Jack-Birtles/IDENTIDEM.design-MRF2/3MF/Main Parts/advance-lever.3mf

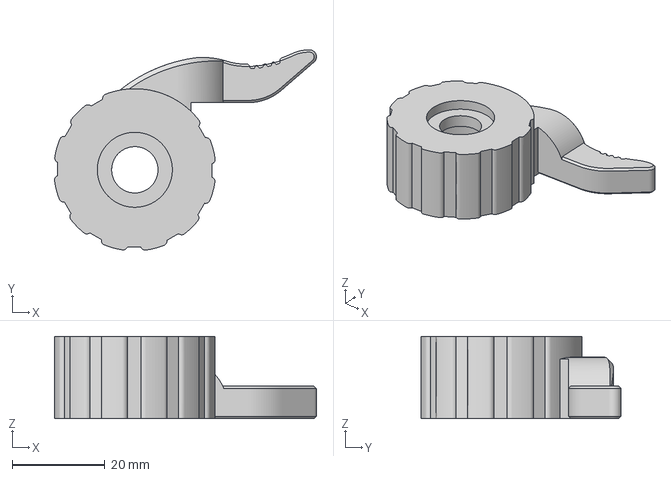
[picture p15: CAD file, 2026-02-24]
3MF/Main Parts/advance-lever.3mf
56.6 x 43.2 x 17.8 mm
