Jack-Birtles/IDENTIDEM.design-MRF2/3MF/Bayonet Lens Cone/lens-center-ring.3mf

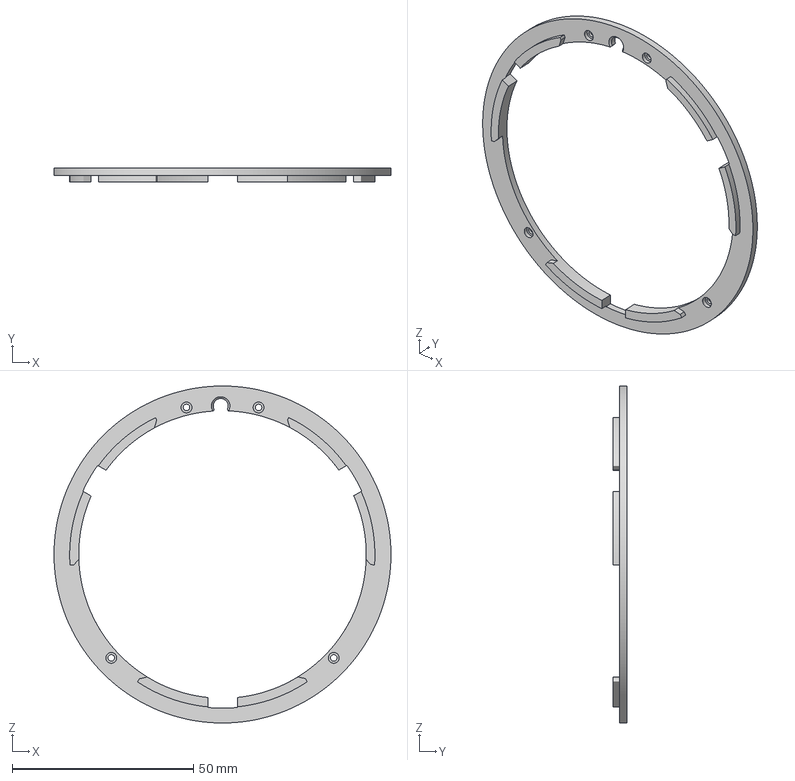
[picture p16: CAD file, 2026-02-24]
3MF/Bayonet Lens Cone/lens-center-ring.3mf
93.0 x 3.75 x 93.0 mm
