Jack-Birtles/IDENTIDEM.design-MRF2/3MF/Film Masks/6x9.3mf

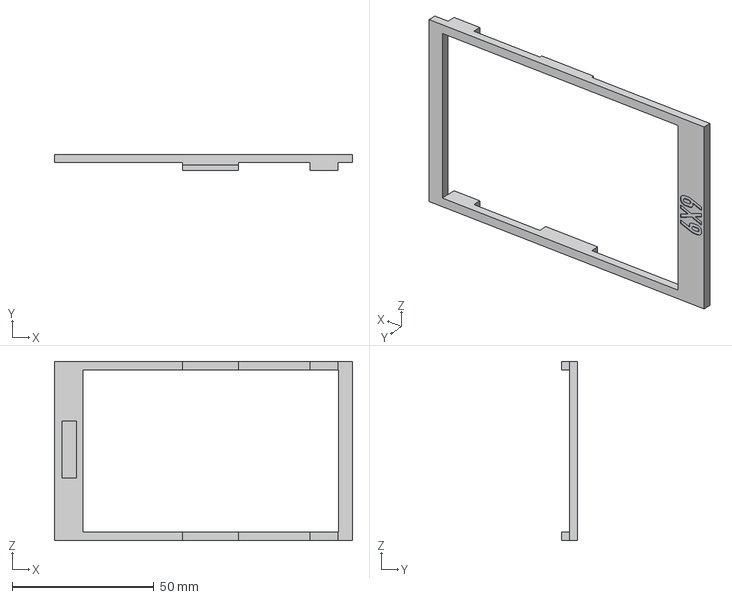
[picture p17: CAD file, 2026-02-24]
3MF/Film Masks/6x9.3mf
105.0 x 5.65 x 63.2 mm
