Jack-Birtles/IDENTIDEM.design-MRF2/3MF/Fine Parts/lidar-sensor-holder.3mf

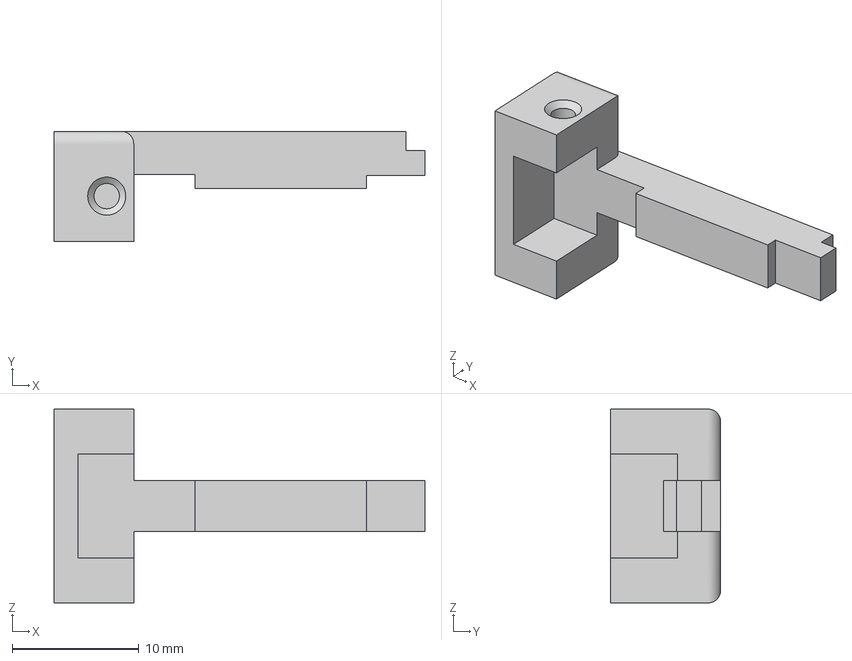
[picture p18: CAD file, 2026-02-24]
3MF/Fine Parts/lidar-sensor-holder.3mf
29.2 x 8.70 x 15.3 mm
