Jack-Birtles/IDENTIDEM.design-MRF2/3MF/Main Parts/middle-plate.3mf

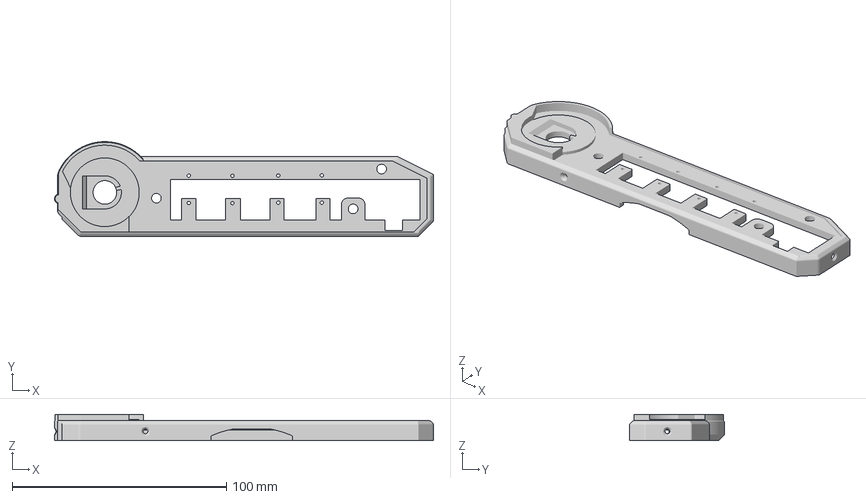
[picture p19: CAD file, 2026-02-24]
3MF/Main Parts/middle-plate.3mf
176.7 x 44.2 x 12.3 mm
