Jack-Birtles/IDENTIDEM.design-MRF2/3MF/Bayonet Lens Cone/lens-top-ring.3mf

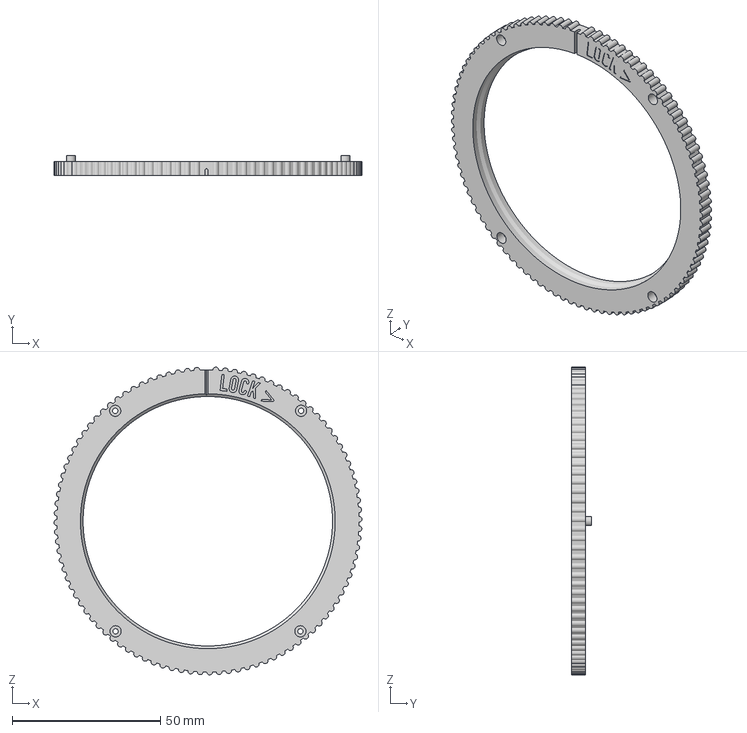
[picture p20: CAD file, 2026-02-24]
3MF/Bayonet Lens Cone/lens-top-ring.3mf
104.0 x 6.83 x 103.9 mm
