Jack-Birtles/IDENTIDEM.design-MRF2/3MF/Fine Parts/spring-ring.3mf

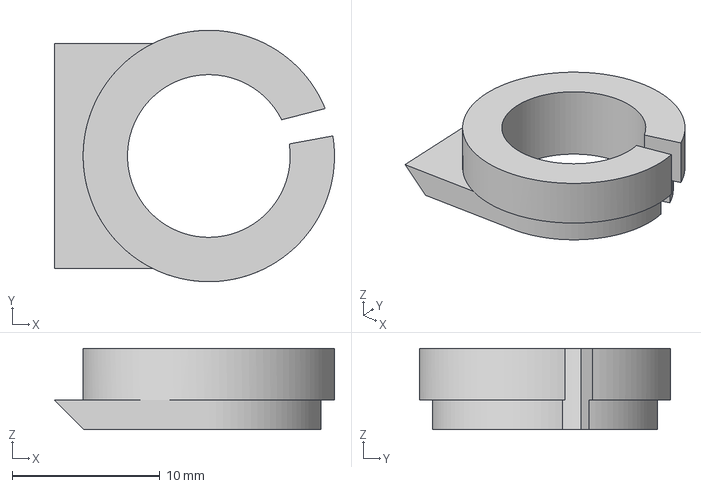
[picture p22: CAD file, 2026-02-24]
3MF/Fine Parts/spring-ring.3mf
18.9 x 17.0 x 5.50 mm
