Jack-Birtles/IDENTIDEM.design-MRF2/3MF/Main Parts/viewfinder-body.3mf

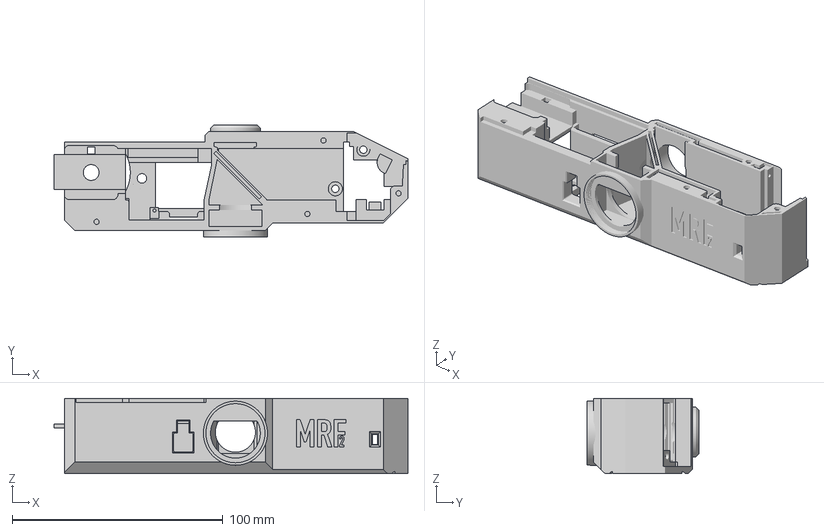
[picture p23: CAD file, 2026-02-24]
3MF/Main Parts/viewfinder-body.3mf
168.0 x 53.1 x 35.6 mm
