Jack-Birtles/IDENTIDEM.design-MRF2/3MF/Fine Parts/advance-post-top.3mf

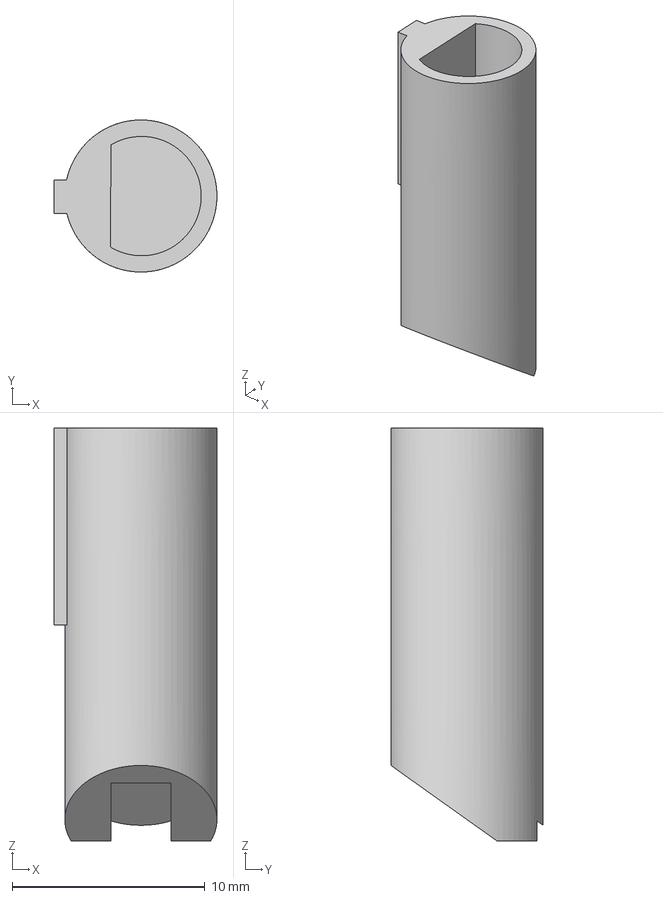
[picture p25: CAD file, 2026-02-24]
3MF/Fine Parts/advance-post-top.3mf
8.46 x 7.90 x 21.5 mm
