Jack-Birtles/IDENTIDEM.design-MRF2/3MF/Main Parts/door-back.3mf

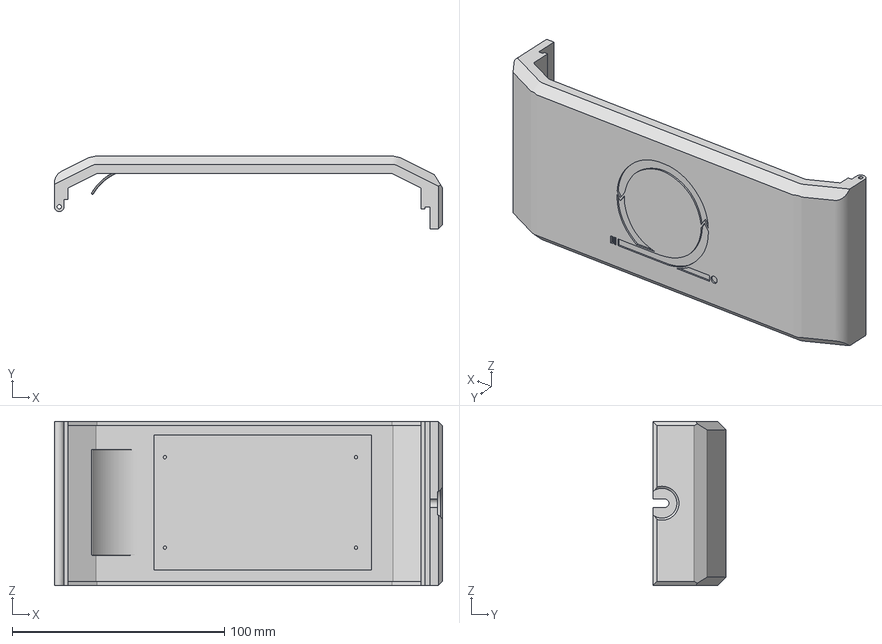
[picture p26: CAD file, 2026-02-24]
3MF/Main Parts/door-back.3mf
182.8 x 34.6 x 77.3 mm
