Jack-Birtles/IDENTIDEM.design-MRF2/3MF/Film Masks/9x3.3mf

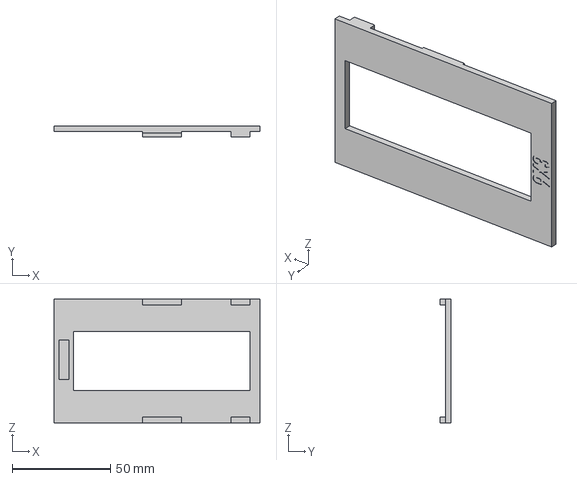
[picture p27: CAD file, 2026-02-24]
3MF/Film Masks/9x3.3mf
105.0 x 5.65 x 63.2 mm
