Jack-Birtles/IDENTIDEM.design-MRF2/3MF/Fine Parts/advance-pin.3mf

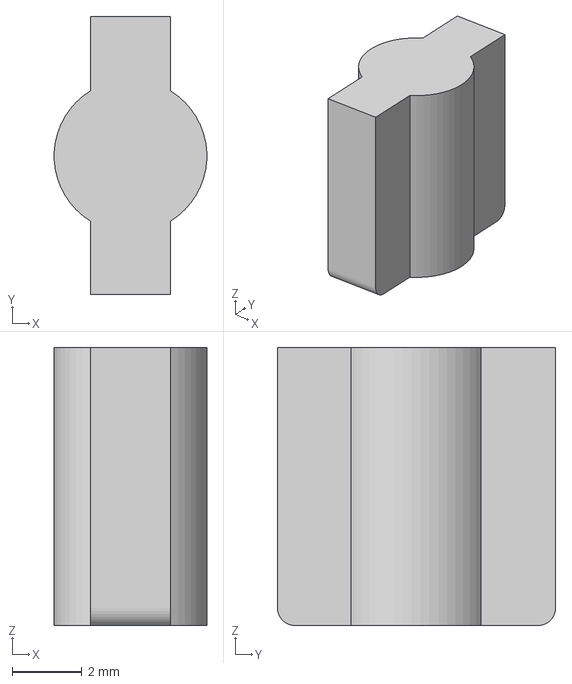
[picture p28: CAD file, 2026-02-24]
3MF/Fine Parts/advance-pin.3mf
4.39 x 8.00 x 8.00 mm
