Jack-Birtles/IDENTIDEM.design-MRF2/3MF/Main Parts/camera-body.3mf

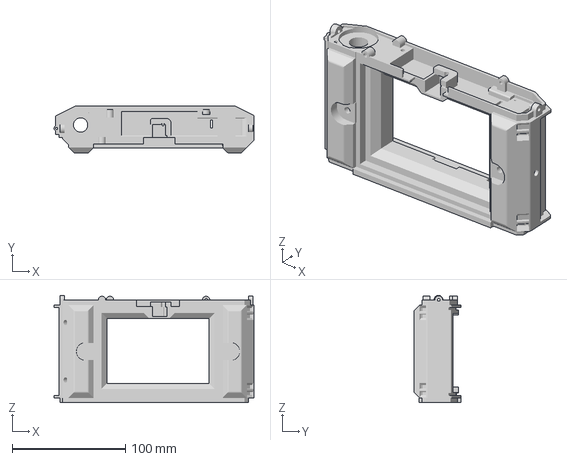
[picture p29: CAD file, 2026-02-24]
3MF/Main Parts/camera-body.3mf
176.7 x 41.5 x 94.8 mm
