Jack-Birtles/IDENTIDEM.design-MRF2/3MF/Fine Parts/advance-spring-cap.3mf

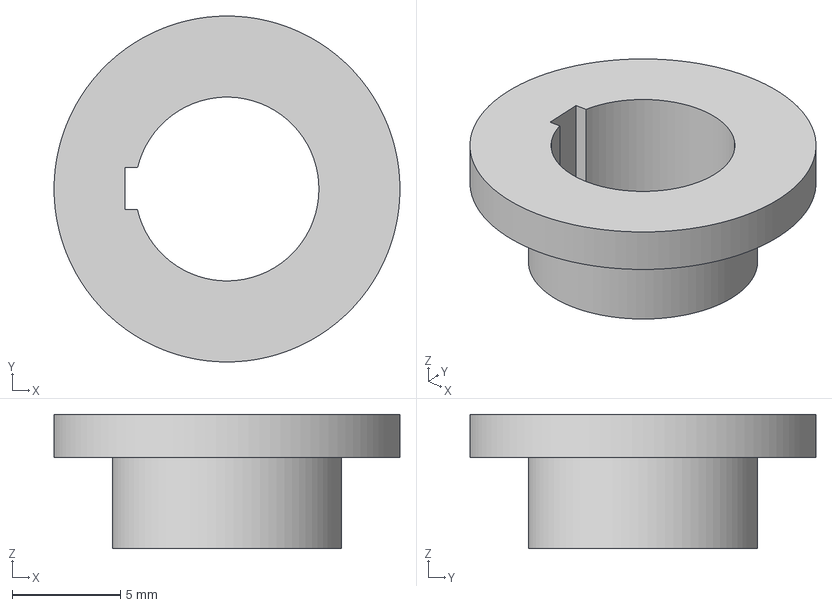
[picture p30: CAD file, 2026-02-24]
3MF/Fine Parts/advance-spring-cap.3mf
16.0 x 16.0 x 6.21 mm
