Jack-Birtles/IDENTIDEM.design-MRF2/3MF/Main Parts/body-bottom.3mf

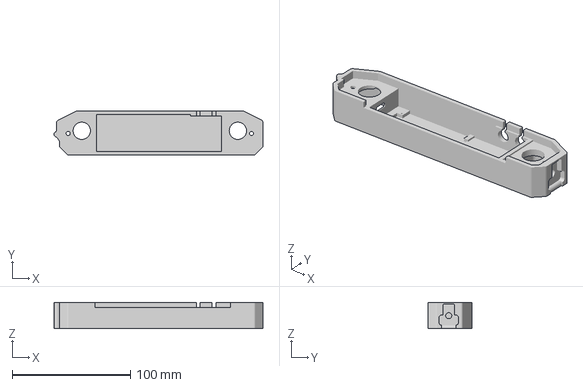
[picture p31: CAD file, 2026-02-07]
3MF/Main Parts/body-bottom.3mf
176.7 x 37.2 x 22.0 mm
