Jack-Birtles/IDENTIDEM.design-MRF2/3MF/Fine Parts/advance-ratchet.3mf

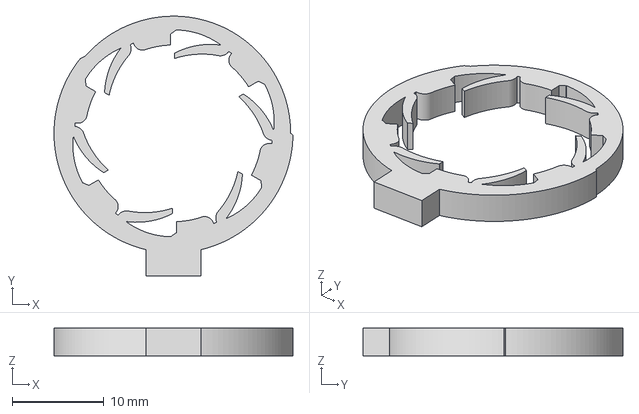
[picture p32: CAD file, 2026-02-24]
3MF/Fine Parts/advance-ratchet.3mf
26.0 x 28.2 x 3.00 mm
