Jack-Birtles/IDENTIDEM.design-MRF2/3MF/Fine Parts/left (from back) spool.3mf

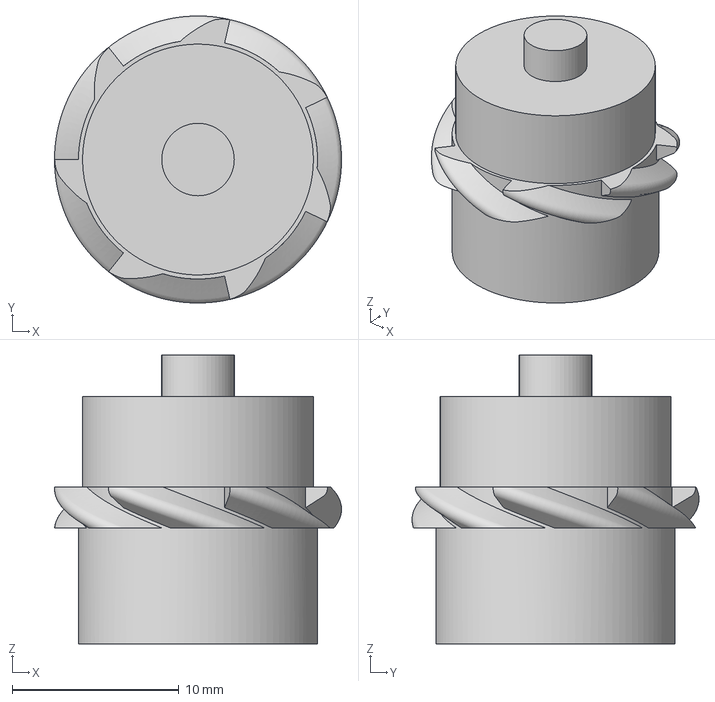
[picture p33: CAD file, 2026-02-24]
3MF/Fine Parts/left (from back) spool.3mf
17.2 x 17.2 x 17.3 mm
