Jack-Birtles/IDENTIDEM.design-MRF2/3MF/Fine Parts/right (from back) spool.3mf

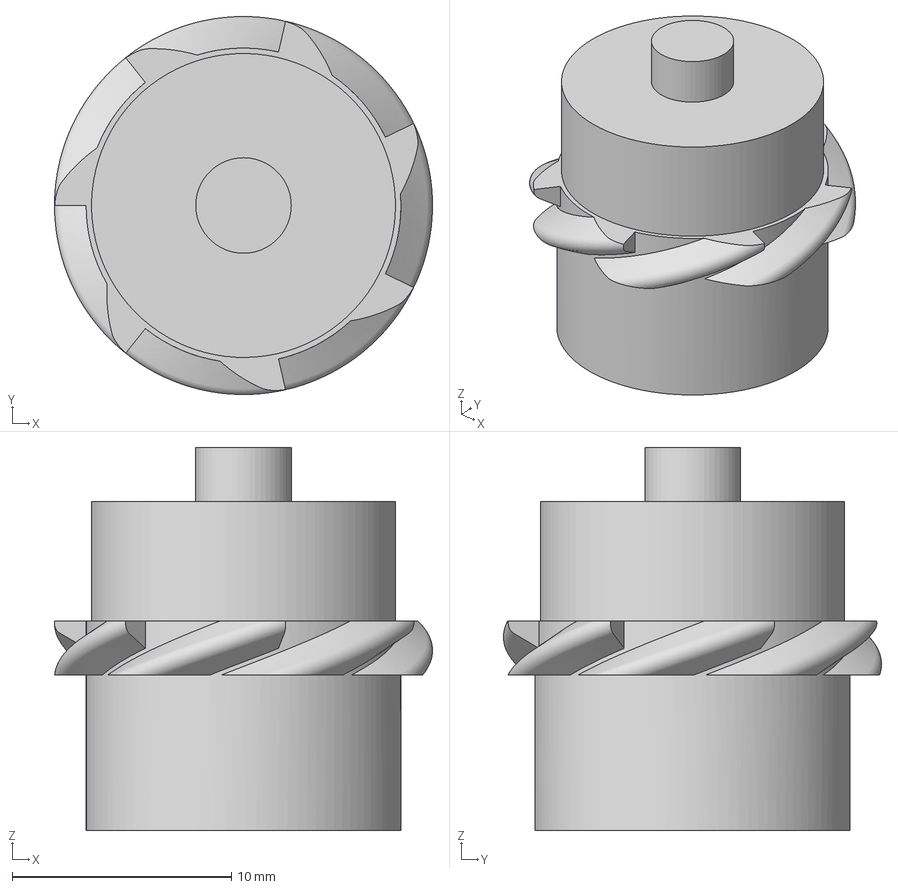
[picture p34: CAD file, 2026-02-24]
3MF/Fine Parts/right (from back) spool.3mf
17.2 x 17.2 x 17.5 mm
