Jack-Birtles/IDENTIDEM.design-MRF2/3MF/Fine Parts/spool-key (optional).3mf

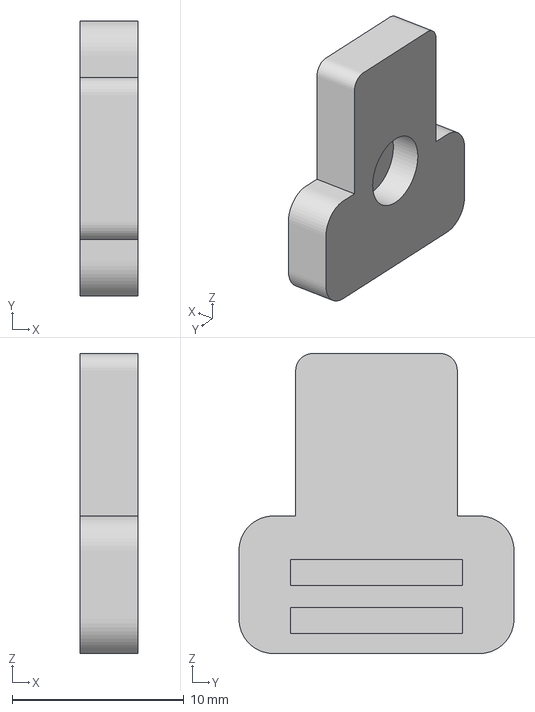
[picture p35: CAD file, 2026-02-24]
3MF/Fine Parts/spool-key (optional).3mf
3.38 x 16.0 x 17.5 mm
