Jack-Birtles/IDENTIDEM.design-MRF2/3MF/Fine Parts/advance-post-bottom.3mf

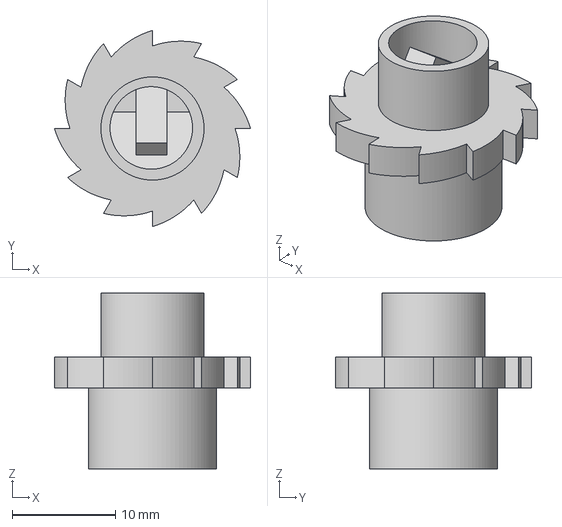
[picture p36: CAD file, 2026-02-24]
3MF/Fine Parts/advance-post-bottom.3mf
19.0 x 19.0 x 17.0 mm
