Jack-Birtles/IDENTIDEM.design-MRF2/Firmware/include/lidar_logic.h

#ifndef LIDAR_LOGIC_H
#define LIDAR_LOGIC_H

#include <stddef.h>
#include <stdint.h>
#include <DTS6012M_UART.h>

struct LidarCandidate
{
  bool valid;
  int distance_cm;
  int confidence;
  int quality_level; // 1..4 (poor..excellent), 0 when invalid
};

// offset_delta_cm is the difference between the configured geometry-offset
// pref and the default it was calibrated with, in cm:
// (lidar_distance_offset_mm - DEFAULT_LIDAR_DISTANCE_OFFSET_MM) / 10.
LidarCandidate chooseBestLidarCandidate(const DTSMeasurement &measurement,
                                        int previous_distance_cm,
                                        bool has_lens_prior,
                                        int lens_prior_cm,
                                        int offset_delta_cm = 0);

int blendLidarDistance(int previous_distance_cm, int next_distance_cm, int confidence);

// SNR in permille: primary intensity relative to the sensor's ambient-light
// baseline (sunlightBase). Returns -1 when there is no baseline (sunlightBase
// == 0), signalling the caller to skip SNR-based logic. Exposed for the
// diagnostics screen and unit tests.
int computeSnrPermille(uint16_t intensity, uint16_t sunlight_base);

// Near-range distance correction (cm). Below LIDAR_CAL_CUTOFF_CM the dToF sensor
// over-reads, so a single-reference power law pulls the value toward truth. The
// correction is bounded: it can never return less than LIDAR_CAL_MIN_OUTPUT_PCT
// percent of the raw distance (interim guard pending the measured table, bd 4p9),
// so real sub-metre subjects are not collapsed below the display floor. Values at
// or above the cutoff pass through unchanged. Exposed for the diagnostics screen
// and unit tests. The correction anchor was measured with the default geometry
// offset; pass offset_delta_cm (configured minus default, in cm) so the
// correction is evaluated in the default-offset frame and the delta re-added,
// keeping the anchor valid when the user tunes the offset pref.
int applyLidarCalibrationCm(int raw_cm, int offset_delta_cm = 0);

// True when the LiDAR reading is so far beyond the lens focus prior that it is
// almost certainly a beam-miss (LiDAR found distant background past the framed
// subject). Asymmetric: only flags overshoot, not undershoot. Returns false
// when the lens is focused beyond the near-range gate threshold or no prior is
// available. The allowed overshoot scales with the prior, since parallax
// beam-miss error grows with distance; a confident return (quality_level >=
// LIDAR_PLAUSIBILITY_TRUST_QUALITY_LEVEL) earns a wider but still finite
// allowance, so a gross overshoot is gated even when graded GOOD/EXCELLENT.
bool isLidarReadingImplausible(int lidar_distance_cm, int lens_prior_cm, int quality_level);

// Running state for the plausibility-gate hold. The gate rejects readings that
// overshoot the lens prior and holds the previous value; this tracks how long
// the current overshoot has persisted and whether the rejected readings are
// settling on a consistent value (a deliberate re-aim) or are jumpy (a true
// beam-miss past the subject).
struct PlausibilityHoldState
{
  int rejectedFrames = 0;   // consecutive implausible frames in this hold
  int consistentFrames = 0; // consecutive implausible frames agreeing with the last
  int lastRejectedCm = 0;   // distance of the previous implausible reading (0 = none yet)
};

// Feed one implausible reading into the hold state and decide whether to release
// (accept) it. Releases when the rejected readings have settled within
// stable_delta_cm for stable_release_frames in a row (deliberate re-aim at a
// real far subject), or when max_hold_frames is reached (safety cap so a noisy
// beam-miss can never pin the readout to a stale value forever).
bool updatePlausibilityHold(PlausibilityHoldState &state,
                            int reading_cm,
                            int stable_delta_cm,
                            int stable_release_frames,
                            int max_hold_frames);

// Clear the hold state. Call when a plausible reading arrives.
void resetPlausibilityHold(PlausibilityHoldState &state);

// Add a confidence boost once the LiDAR has locked onto a stable subject
// (consecutive frames within LIDAR_STABLE_DELTA_CM of each other). Caller
// tracks the streak count; this function applies the boost and clamps the
// result so a marginal reading cannot be promoted to excellent.
int applyStableConfidenceBoost(int base_confidence, int stable_streak_frames);

// Hysteresis-based update for the "ambient IR is high enough to degrade the
// LiDAR" warning state. Caller passes the current state and the sensor's
// sunlight base; returns the next state. Stays on between EXIT and ENTER
// thresholds so the indicator does not flicker.
bool updateSunlightWarnState(bool currently_warning, uint16_t sunlight_base);

void formatDistanceDisplay(int corrected_cm, char *buffer, size_t bufferSize);

// Placeholder shown when the sensor stops returning data. "Inf?" when the last
// accepted reading was at or beyond LIDAR_FAR_SIGNAL_LOSS_CM — no return at
// that range usually means the user re-aimed at the sky — and "..." otherwise.
// Deliberately distinct from the "Inf." that formatDistanceDisplay() emits for
// a genuine measured reading, so a dropout can't be read as a measurement.
// current_display is the string currently on screen: once it already marks a far
// dropout ("Inf?"/"Inf."), the placeholder stays "Inf?" so the far state survives
// clearLidarDisplay() zeroing prev_distance between frames. Pass nullptr to decide
// purely from prev_distance_cm.
const char *lidarSignalLossPlaceholder(int prev_distance_cm, const char *current_display);

// Format the age of the last LiDAR telemetry frame for the diagnostics screen:
// "--" when no frame has been captured yet (telemetry_ms == 0 sentinel),
// "NNNms" under one second, "N.Ns" up to 99s, ">99s" beyond. Takes uint32_t so
// the unsigned subtraction survives a millis() wrap on target and host alike.
void formatLidarTelemetryAge(uint32_t now_ms, uint32_t telemetry_ms, char *buffer, size_t bufferSize);

#endif // LIDAR_LOGIC_H
