Jack-Birtles/IDENTIDEM.design-MRF2/Firmware/src/lidar_recovery_logic.cpp

#include "lidar_recovery_logic.h"

#include <Arduino.h>

#include "mrfconstants.h"

namespace
{
unsigned long computeRecoveryBackoffMs(int consecutiveErrors)
{
  unsigned long delayMs = LIDAR_RECOVERY_RETRY_BASE_MS;
  int attempts = min(consecutiveErrors, 6);
  for (int i = 1; i < attempts; i++)
  {
    delayMs = min(delayMs * 2UL, LIDAR_RECOVERY_RETRY_MAX_MS);
  }
  return delayMs;
}
} // namespace

LidarRecoveryEvent lidarRecoveryEventForUpdateError(DTSError update_error)
{
  // NO_NEW_DATA (v2.6.0+) is returned whenever no complete frame arrived this
  // poll — the normal case every time the loop runs faster than the sensor's
  // frame rate. Like a genuine TIMEOUT it must map to the TIME-based TIMEOUT
  // event, which only escalates to recovery after LIDAR_RECOVERY_TIMEOUT_MS of no
  // valid data. It must NOT map to the COUNT-based ERROR event: three fast no-data
  // polls would otherwise cross LIDAR_RECOVERY_ERROR_THRESHOLD in milliseconds and
  // trip spurious recovery on a perfectly healthy sensor. Real frame faults (CRC,
  // framing, buffer overflow) still map to ERROR.
  switch (update_error)
  {
    case DTSError::NO_NEW_DATA:
    case DTSError::TIMEOUT:
      return LidarRecoveryEvent::TIMEOUT;
    default:
      return LidarRecoveryEvent::ERROR;
  }
}

void resetLidarRecoveryState(LidarRecoveryState &state, unsigned long now_ms)
{
  state.initialized = true;
  state.recovering = false;
  state.consecutive_errors = 0;
  state.last_valid_measurement_ms = now_ms;
  state.last_frame_ms = now_ms;
  state.next_recovery_attempt_ms = now_ms;
}

LidarRecoveryDecision updateLidarRecoveryState(
    LidarRecoveryState &state, LidarRecoveryEvent event, unsigned long now_ms)
{
  if (!state.initialized)
  {
    resetLidarRecoveryState(state, now_ms);
  }

  if (event == LidarRecoveryEvent::VALID_MEASUREMENT)
  {
    state.recovering = false;
    state.consecutive_errors = 0;
    state.last_valid_measurement_ms = now_ms;
    state.last_frame_ms = now_ms;
    state.next_recovery_attempt_ms = now_ms;
    return {false, false};
  }

  if (event == LidarRecoveryEvent::NO_VALID_MEASUREMENT)
  {
    // A well-formed frame arrived but its candidate was gated out. The link
    // is healthy, so stand recovery down — but leave
    // last_valid_measurement_ms alone so the display still goes stale.
    state.recovering = false;
    state.consecutive_errors = 0;
    state.last_frame_ms = now_ms;
  }
  else if (event == LidarRecoveryEvent::ERROR)
  {
    state.consecutive_errors++;
    // Arm the deadline only on the transition into recovery: during a
    // sustained outage every poll lands here, and rewriting the deadline each
    // time clobbered the failed-attempt backoff set by
    // noteLidarRecoveryAttemptResult, hammering reset/enable at poll cadence.
    if (state.consecutive_errors >= LIDAR_RECOVERY_ERROR_THRESHOLD && !state.recovering)
    {
      state.recovering = true;
      state.next_recovery_attempt_ms = now_ms;
    }
  }
  else if (event == LidarRecoveryEvent::TIMEOUT)
  {
    if ((now_ms - state.last_frame_ms) > LIDAR_RECOVERY_TIMEOUT_MS && !state.recovering)
    {
      state.recovering = true;
      state.next_recovery_attempt_ms = now_ms;
    }
  }

  bool clearDisplay = (now_ms - state.last_valid_measurement_ms) > LIDAR_NO_DATA_TIMEOUT_MS;
  // Signed-difference compare so the deadline survives millis() rollover.
  bool attemptRecovery = state.recovering &&
                         static_cast<long>(now_ms - state.next_recovery_attempt_ms) >= 0;
  return {clearDisplay, attemptRecovery};
}

void noteLidarRecoveryAttemptResult(LidarRecoveryState &state, bool success, unsigned long now_ms)
{
  if (!state.initialized)
  {
    resetLidarRecoveryState(state, now_ms);
  }

  if (success)
  {
    state.recovering = false;
    state.consecutive_errors = 0;
    state.last_valid_measurement_ms = now_ms;
    state.next_recovery_attempt_ms = now_ms;
    return;
  }

  state.recovering = true;
  state.consecutive_errors = min(state.consecutive_errors + 1, 10);
  state.next_recovery_attempt_ms = now_ms + computeRecoveryBackoffMs(state.consecutive_errors);
}
