Jack-Birtles/IDENTIDEM.design-MRF2/Firmware/include/interface.h

#ifndef INTERFACE_H
#define INTERFACE_H

// Functions to draw UI
// ---------------------
void drawMainUI();
void drawConfigUI();
void drawFilmConfigUI();
void drawFrameTuningConfigUI();
void drawLensConfigUI();
void drawMeterConfigUI();
void drawLidarConfigUI();
void drawLidarDiagnosticsUI();
void drawDisplayConfigUI();
void drawHorizonTrimConfigUI();
void drawCalibUI();
void drawCalibCompleteUI();
void drawResetConfirmUI();
void drawFactoryResetConfirmUI();
void drawHealthUI();
void drawReticleAdjustUI();
void drawExternalUI();
void drawSleepUI();
// ---------------------

#endif // INTERFACE_H
