Jack-Birtles/IDENTIDEM.design-MRF2/Firmware/src/lenses.cpp

#include "lenses.h"
#include <stddef.h> // For size_t

// Lens and film format definitions
Lens lenses[] = {
    {5063, "50/6.3", 50.0, {0, 0, 0, 0, 0, 0, 0, 0, 0, 0}, {1, 1.2, 1.5, 2, 3, 5, 10, 0, 0, 0}, {0, 6.3, 8, 11, 16, 22, 32, 0, 0}, {0, 17, 128, 109}, false},
    {6563, "65/6.3", 65.0, {261, 268, 276, 287, 299, 312, 330, 0, 0, 0}, {1, 1.2, 1.5, 2, 3, 5, 10, 0, 0, 0}, {0, 6.3, 8, 11, 16, 22, 32, 0, 0}, {0, 17, 128, 109}, true},
    {7556, "75/5.6", 75.0, {0, 0, 0, 0, 0, 0, 0, 0, 0, 0}, {1, 1.2, 1.5, 2, 3, 5, 10, 0, 0, 0}, {0, 5.6, 8, 11, 16, 22, 32, 45, 0}, {9, 24, 110, 95}, false},
    {9035, "90/3.5", 90.0, {0, 0, 0, 0, 0, 0, 0, 0, 0, 0}, {1, 1.2, 1.5, 2, 3, 5, 10, 0, 0, 0}, {3.5, 4, 5.6, 8, 11, 16, 22, 32, 0}, {18, 32, 92, 79}, false},
    {10035, "100/3.5", 100.0, {0, 0, 0, 0, 0, 0, 0, 0, 0, 0}, {1, 1.2, 1.5, 2, 3, 5, 10, 0, 0, 0}, {3.5, 4, 5.6, 8, 11, 16, 22, 32, 0}, {23, 36, 84, 71}, false},
    {10028, "100/2.8", 100.0, {0, 0, 0, 0, 0, 0, 0, 0, 0, 0}, {1, 1.2, 1.5, 2, 3, 5, 10, 0, 0, 0}, {2.8, 4, 5.6, 8, 11, 16, 22, 32, 0}, {23, 36, 84, 71}, false},
    {12747, "127/4.7", 127.0, {0, 0, 0, 0, 0, 0, 0, 0, 0, 0}, {1, 1.2, 1.5, 2, 3, 5, 10, 0, 0, 0}, {4.7, 5.6, 8, 11, 16, 22, 32, 45, 64}, {31, 43, 66, 57}, false},
    {15056, "150/5.6", 150.0, {0, 0, 0, 0, 0, 0, 0, 0, 0, 0}, {2, 2.5f, 3, 5, 10, 0, 0, 0, 0, 0}, {5.6, 8, 11, 16, 22, 32, 45, 0, 0}, {36, 48, 56, 47}, false},
    {25005, "250/5.0", 250.0, {0, 0, 0, 0, 0, 0, 0, 0, 0, 0}, {2.5f, 4, 5, 7, 8, 10, 15, 20, 30, 50}, {5, 8, 11, 16, 22, 32, 45, 0, 0}, {47, 57, 34, 29}, false},
    {25008, "250/8.0", 250.0, {0, 0, 0, 0, 0, 0, 0, 0, 0, 0}, {3.5f, 4, 5, 7, 10, 15, 20, 30, 50, 0}, {8, 11, 16, 22, 32, 45, 64, 0, 0}, {47, 57, 34, 29}, false}
};

const size_t NUM_LENSES = sizeof(lenses) / sizeof(lenses[0]);

int getLensDistancePointCount(const Lens &lens)
{
  int point_count = 0;
  float previous_distance = 0.0f;

  for (int i = 0; i < LENS_DISTANCE_POINT_COUNT; i++)
  {
    float distance_marker = lens.distance[i];
    if (distance_marker <= 0.0f)
    {
      break;
    }

    if (point_count > 0 && distance_marker <= previous_distance)
    {
      break;
    }

    previous_distance = distance_marker;
    point_count++;
  }

  return point_count;
}
